Ismael034/usbsp/hardware/usb_sp_fp/usb_sp_model/SOT-666-6_L1.6-W1.2-P0.50-LS1.6-BL.step

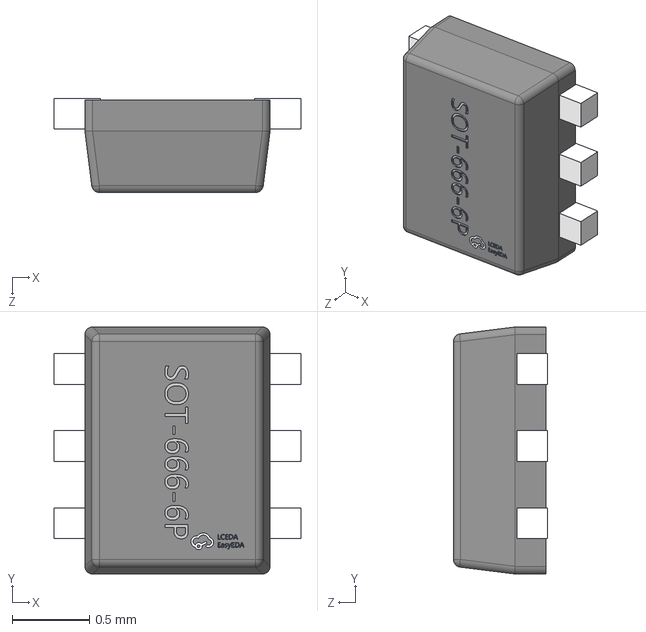
[picture p16: CAD file, 2025-09-13]
hardware/usb_sp_fp/usb_sp_model/SOT-666-6_L1.6-W1.2-P0.50-LS1.6-BL.step
1.60 x 1.60 x 0.611 mm
