Ismael034/usbsp/hardware/usb_sp_fp/usb_sp_model/USB-C-SMD_KH-TYPE-C-16P.step

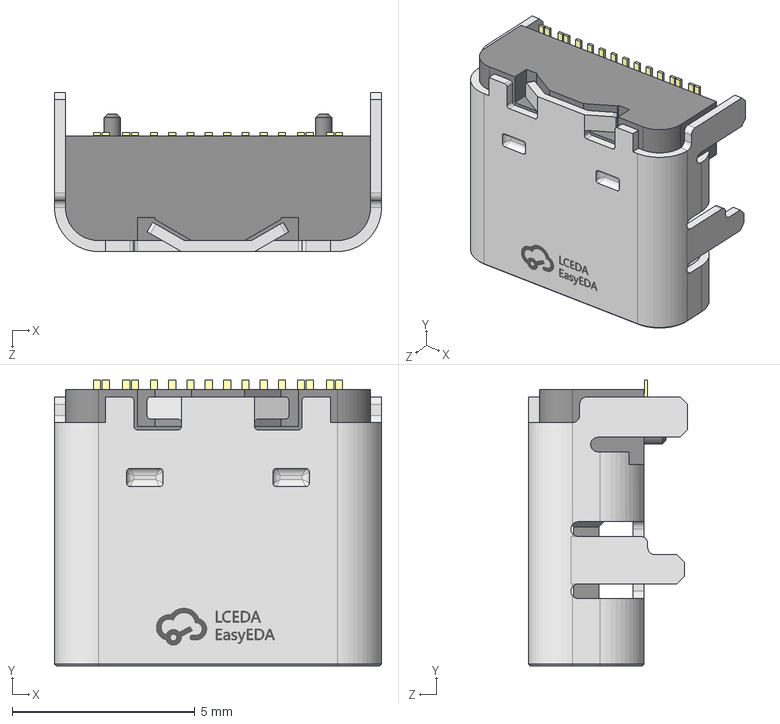
[picture p17: CAD file, 2025-09-13]
hardware/usb_sp_fp/usb_sp_model/USB-C-SMD_KH-TYPE-C-16P.step
8.94 x 7.81 x 4.35 mm
