Ismael034/usbsp/hardware/usb_sp_fp/usb_sp_model/CRYSTAL-SMD_4P-L3.2-W2.5-BL.step

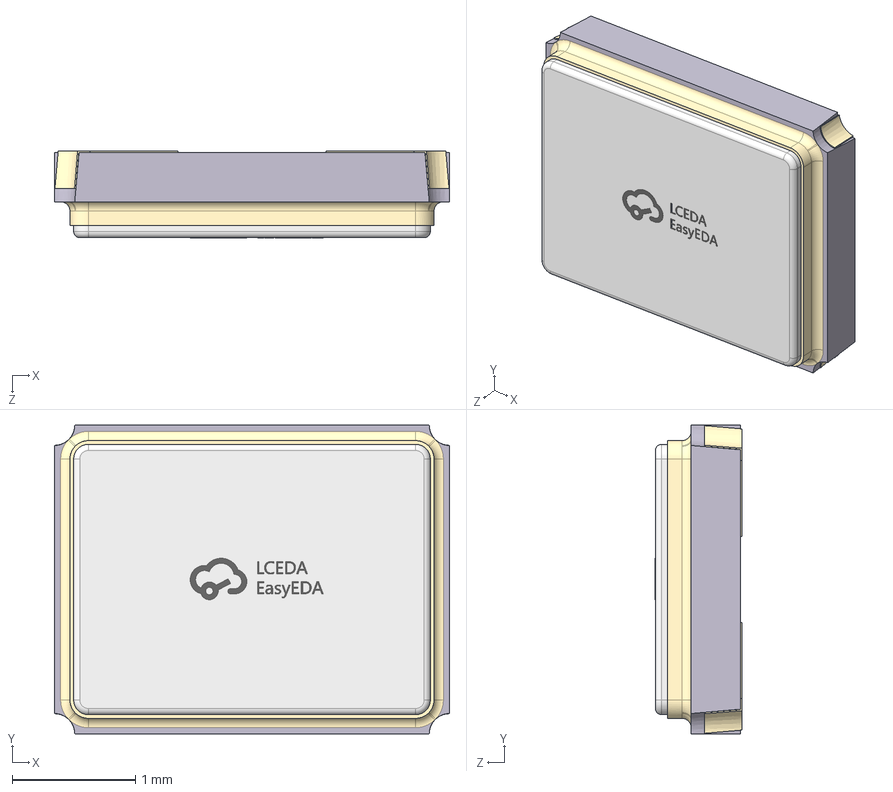
[picture p18: CAD file, 2025-09-13]
hardware/usb_sp_fp/usb_sp_model/CRYSTAL-SMD_4P-L3.2-W2.5-BL.step
3.20 x 2.50 x 0.701 mm
