Ismael034/usbsp/hardware/usb_sp_fp/usb_sp_model/CRYSTAL-SMD_L3.2-W1.5-1.step

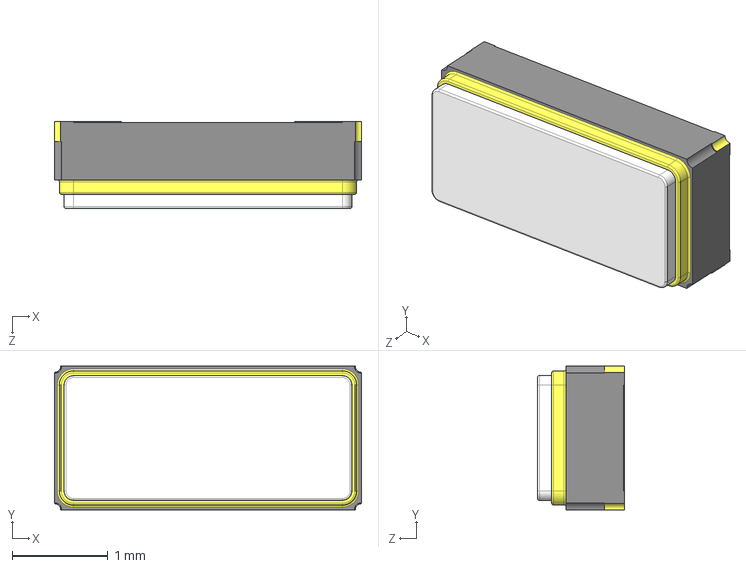
[picture p19: CAD file, 2025-09-13]
hardware/usb_sp_fp/usb_sp_model/CRYSTAL-SMD_L3.2-W1.5-1.step
3.20 x 1.50 x 0.91 mm
