Ismael034/usbsp/hardware/usb_sp_fp/usb_sp_model/UDFN-8_L3.0-W2.0-P0.50-BL-EP-3.step

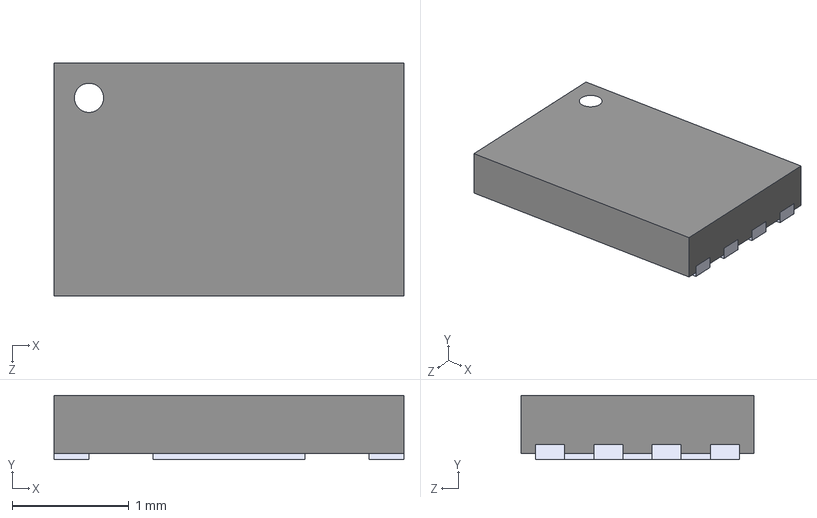
[picture p20: CAD file, 2025-09-13]
hardware/usb_sp_fp/usb_sp_model/UDFN-8_L3.0-W2.0-P0.50-BL-EP-3.step
3.00 x 0.55 x 2.00 mm
