Ismael034/usbsp/hardware/usb_sp_fp/usb_sp_model/TQFN-48_L7.0-W7.0-P0.50-BL-EP5.5.step

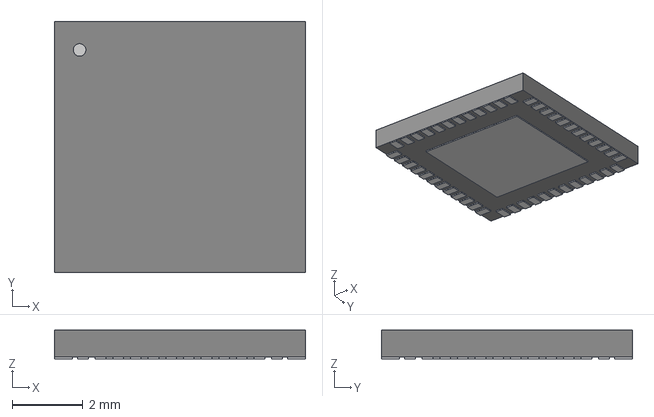
[picture p22: CAD file, 2025-09-13]
hardware/usb_sp_fp/usb_sp_model/TQFN-48_L7.0-W7.0-P0.50-BL-EP5.5.step
7.11 x 7.11 x 0.815 mm
