Ismael034/usbsp/hardware/usb_sp_fp/usb_sp_model/SW-SMD_L3.9-W3.0-P4.45.step

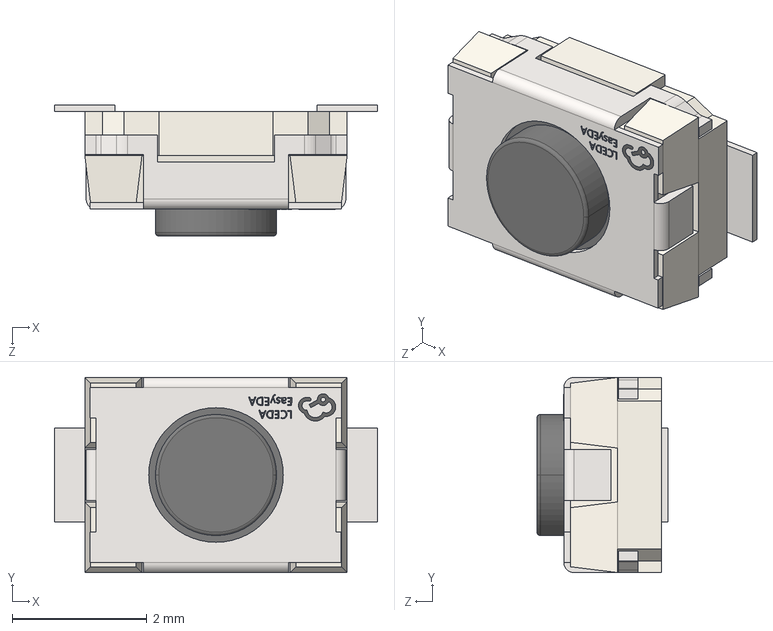
[picture p23: CAD file, 2025-09-13]
hardware/usb_sp_fp/usb_sp_model/SW-SMD_L3.9-W3.0-P4.45.step
4.80 x 2.90 x 1.95 mm
