Ismael034/usbsp/hardware/usb_sp_fp/usb_sp_model/QFN-20_L3.0-W3.0-P0.40-TL-EP1.7.step

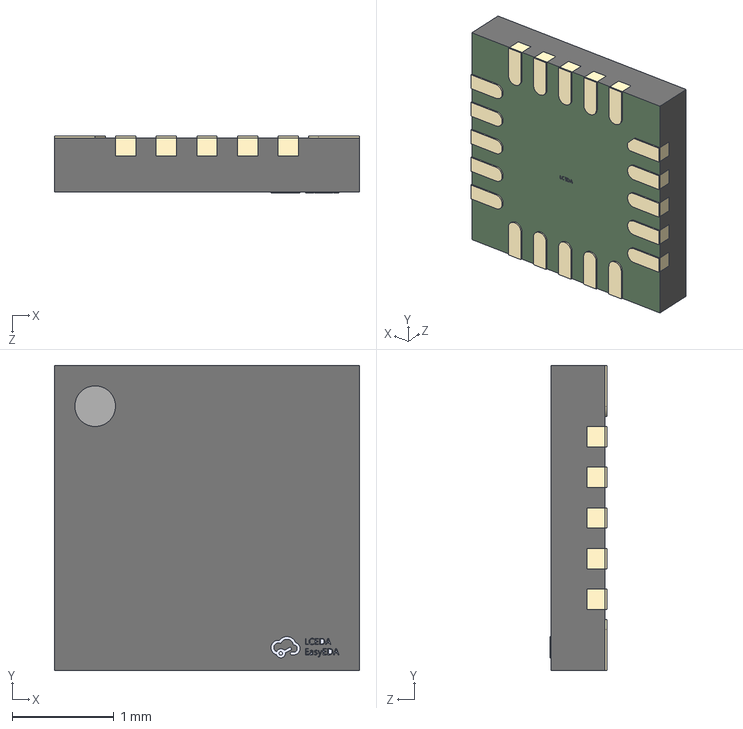
[picture p24: CAD file, 2025-09-13]
hardware/usb_sp_fp/usb_sp_model/QFN-20_L3.0-W3.0-P0.40-TL-EP1.7.step
3.00 x 3.00 x 0.565 mm
